jdg511/quadpreandrecorder/hardware/snapshots/hardware_snapshot_step1_before_via_resize_20260801_083059/manufacturing/QuadPreRecorder-drill-report.txt

Drill report for QuadPreRecorder.kicad_pcb
Created on 2026-07-25T09:17:04

Copper Layer Stackup:
    =============================================================
    L1 :  F.Cu                      front
    L2 :  B.Cu                      back

Drill file 'QuadPreRecorder-PTH.drl' contains
    plated through holes:
    =============================================================
    T1  0.400mm  0.0157"  (152 holes))
    T2  1.000mm  0.0394"  (137 holes)  (with 5 slots)
    T3  1.200mm  0.0472"  (4 holes))
    T4  1.300mm  0.0512"  (4 holes))
    T5  1.500mm  0.0591"  (8 holes)  (with 2 slots)
    T6  1.600mm  0.0630"  (3 holes))
    T7  1.850mm  0.0728"  (5 holes))

    Total plated holes count 313

Drill file 'QuadPreRecorder-NPTH.drl' contains
    unplated through holes:
    =============================================================
    T1  2.000mm  0.0787"  (2 holes))
    T2  3.000mm  0.1181"  (1 hole)
    T3  3.200mm  0.1260"  (8 holes))

    Total unplated holes count 11
