jdg511/quadpreandrecorder/hardware/QuadPreRecorder-enclosure-labeled-views.pdf

# QuadPreRecorder Rev C3

Enclosure preview with all ports and controls labeled. Hammond 1590XX, 145.2 x 121.2 x 39.3 mm.

### Illicit Apothecary

Face | Ref | Function
Lid | TFT | 3.5 inch capacitive touch display (MSP3526), near-flush window 85.5 x 56 mm
Lid | SW2 | Record button
Lid | SW3 | Rotary encoder, push + turn
Lid | SW4 | 5-way navigation switch (tilt 4 ways + press)
Front | J4 | 1/4 inch line output (Neutrik locking jack)
Front | D4 / D5 | Status LEDs (red / green)
Rear | J1 | 9 V DC input, barrel jack
Rear | J9 | USB-C, charging + data
Rear | SD | Micro-SD card slot (Teensy)
Left | J2 | CAT6 microphone input, shielded RJ45, 4 balanced channels + shield
Right | J5 | 3.5 mm headphone output

Positions are taken from the routed Rev C3 board. Wall-feature heights are approximate for illustration; drilling is done from the 1:1 printed templates, not from this document. An interactive 3D version of this model is available as an HTML file that opens in any web browser.

### Front three-quarter view

### Rear three-quarter view

### Top (lid controls and display)

### Front wall: J4 line out, D4/D5 status LEDs

### Rear wall: J1 9V DC, J9 USB-C, micro-SD

### Left wall: J2 CAT6 mic input

### Right wall: J5 headphone out
