jdg511/quadpreandrecorder/hardware/snapshots/hardware_snapshot_step1_before_via_resize_20260801_083059/exports/QuadPreRecorder-isometric.png

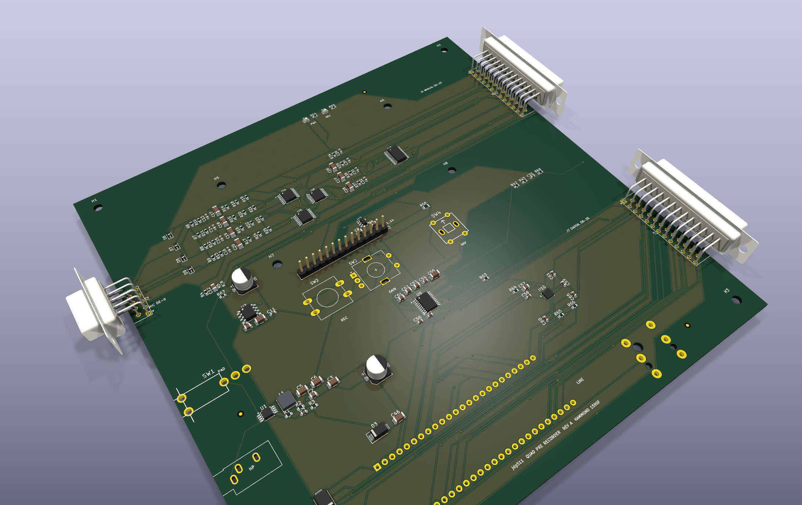
hardware/snapshots/hardware_snapshot_step1_before_via_resize_20260801_083059/exports/QuadPreRecorder-isometric.png
