jdg511/quadpreandrecorder/hardware/snapshots/hardware_snapshot_step1_before_via_resize_20260801_083059/manufacturing/QuadPreRecorder-assembly-bottom.pdf

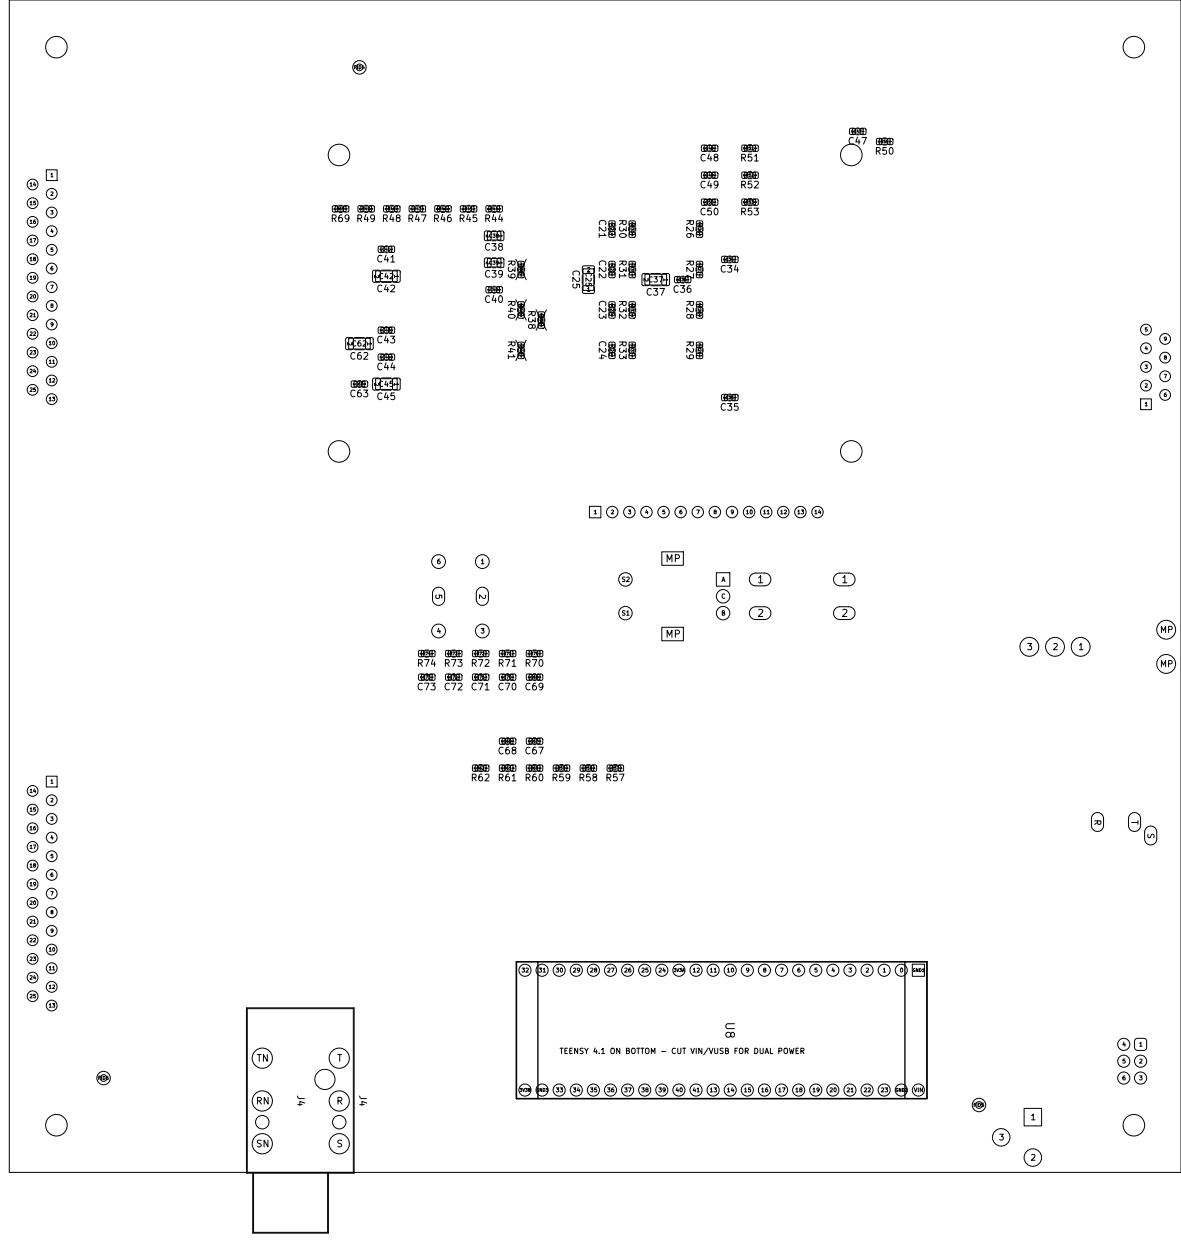
[picture p28: page 1]

1 TEENSY 4.1 ON BOTTOM - CUT VIN/VUSB FOR DUAL POWER
