jdg511/quadpreandrecorder/hardware/snapshots/hardware_snapshot_step1_before_via_resize_20260801_083059/manufacturing/QuadPreRecorder-assembly-top.pdf

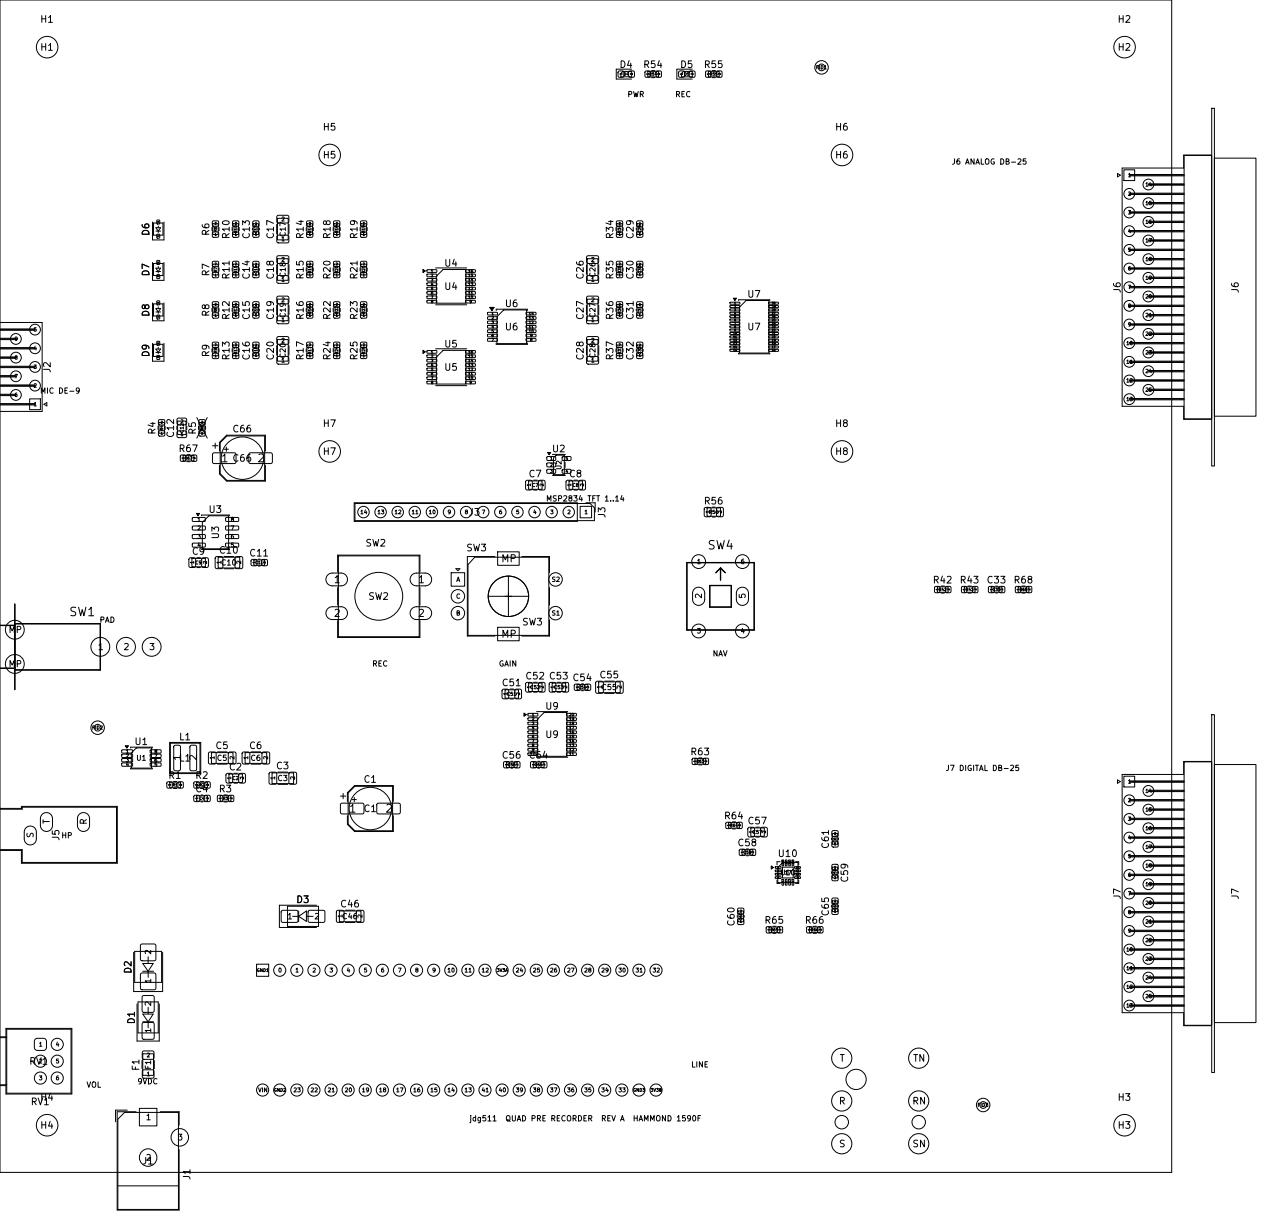
[picture p33: page 1]

jdg511 QUAD PRE RECORDER REV A HAMMOND 1590F
