jdg511/quadpreandrecorder/tools/build_manufacturing.py

"""Generate the checked PCBWay fabrication and assembly handoff.

This script intentionally depends only on Python's standard library and the
KiCad 10 command-line tools.  Run it from any directory with:

    python tools/build_manufacturing.py
"""

from __future__ import annotations

import csv
import hashlib
import os
from pathlib import Path
import shutil
import subprocess
import zipfile


ROOT = Path(__file__).resolve().parents[1]
HARDWARE = ROOT / "hardware"
SCHEMATIC = HARDWARE / "QuadPreRecorder.kicad_sch"
BOARD = HARDWARE / "QuadPreRecorder.kicad_pcb"
OUT = HARDWARE / "manufacturing"
GERBERS = OUT / "gerbers"
EXPORTS = HARDWARE / "exports"
FAB = HARDWARE / "fabrication"
KICAD_CLI = Path(os.environ.get("KICAD_CLI", "")) if os.environ.get("KICAD_CLI") else (
    Path(os.environ.get("LOCALAPPDATA", "")) / "Programs" / "KiCad" / "10.0" / "bin" / "kicad-cli.exe"
)


def run(*args: str, capture: bool = False) -> str:
    command = [str(KICAD_CLI), *args]
    result = subprocess.run(
        command,
        cwd=ROOT,
        check=True,
        text=True,
        capture_output=capture,
    )
    return result.stdout if capture else ""


def drc_is_manufacturing_acceptable(report: str) -> bool:
    """Allow only assembly-courtyard DRC errors; block electrical/fab issues."""

    if "Found 0 unconnected pads" not in report:
        return False
    violation_kinds = {
        line.split("]", 1)[0][1:]
        for line in report.splitlines()
        if line.startswith("[") and "]:" in line
    }
    return not violation_kinds or violation_kinds <= {"courtyards_overlap"}


def reset_generated_directory(path: Path) -> None:
    resolved = path.resolve()
    if ROOT.resolve() not in resolved.parents:
        raise RuntimeError(f"Refusing to reset path outside repository: {resolved}")
    if resolved.exists():
        shutil.rmtree(resolved)
    resolved.mkdir(parents=True)


def build_cpl() -> None:
    raw = OUT / "QuadPreRecorder-CPL-KiCad.csv"
    run(
        "pcb", "export", "pos", "--format", "csv", "--units", "mm",
        "--side", "both", "--exclude-dnp", "-o", str(raw), str(BOARD),
    )
    with raw.open(newline="", encoding="utf-8-sig") as source:
        rows = list(csv.DictReader(source))

    normalized = OUT / "QuadPreRecorder-CPL-PCBWay.csv"
    with normalized.open("w", newline="", encoding="utf-8-sig") as target:
        writer = csv.DictWriter(
            target,
            fieldnames=["Designator", "Mid X", "Mid Y", "Layer", "Rotation"],
        )
        writer.writeheader()
        for row in rows:
            writer.writerow({
                "Designator": row["Ref"],
                "Mid X": f'{float(row["PosX"]):.4f}mm',
                "Mid Y": f'{float(row["PosY"]):.4f}mm',
                "Layer": "Top" if row["Side"].lower() == "top" else "Bottom",
                "Rotation": f'{float(row["Rot"]):.2f}',
            })


# 2026-09-06: parts PCBWay must fit or supply that are NOT placement lines in
# the KiCad BOM/CPL - the U8 socket sub-assembly, and loose off-board parts to
# quote and ship with the boards. Written as a separate CSV so the CPL import
# is not confused by designators that have no placement.
EXTRA_PARTS: list[tuple[str, str, str, str, str, str]] = [
    # designator/role, description, manufacturer, MPN, qty per board, note
    ("U8 (socket)", "1x24 low-profile female socket strip, 2.54 mm, 4.57 mm profile",
     "Samtec", "SLW-124-01-G-S", "2",
     "Solder BOTH strips into the U8 footprint (bottom side, rows at 17.78 mm). "
     "Then plug the Teensy into them - see U8 (module)."),
    ("U8 (module)", "Teensy 4.1 WITH pins pre-soldered (outer 2x24 rows)",
     "PJRC", "TEENSY41_PINS", "1",
     "Plug into the two SLW-124 sockets, microSD slot toward the board edge marked "
     "'SD CARD SLOT THIS EDGE'. Customer-supplied if PCBWay cannot source PJRC. "
     "TEENSY41_NE_PINS (no Ethernet chip) is an acceptable substitute."),
    ("TFT (loose)", "LCDWiki MSP3526 3.5in IPS SPI TFT 320x480, ST7796U, FT6336U CAPACITIVE touch, 14-pin header",
     "LCDWiki / QDtech", "MSP3526", "1",
     "OFF-BOARD, ship loose - do NOT solder; it plugs into the J3 socket. NOT the "
     "MSP3520 (resistive). Please quote; customer will supply if unavailable."),
    ("TFT standoffs (loose)", "M3 x 11 mm brass standoff, female-female, + 8x M3x6 screws",
     "generic", "M3x11 F-F", "4",
     "OFF-BOARD, ship loose. Mounts the TFT over H5-H8 (socket 8.5 mm + header body 2.5 mm)."),
    ("USB D+/D- wires", "2x ~20 mm 30 AWG wire, TP1/TP2 (bottom) to the Teensy 4.1 underside 'USB Device' D+ / D- pads",
     "-", "-", "2",
     "ASSEMBLY STEP: solder the two wires to the Teensy's underside D+/D- pads and to TP1 (D+) / TP2 (D-) "
     "before plugging the Teensy into its sockets. Also CUT the Teensy's VIN-VUSB link pad. "
     "Keep the wires short and together."),
    ("Battery (loose, customer-supplied)", "3.7 V 1S LiPo pouch 906090 (9 x 60 x 90 mm) 5000 mAh WITH protection circuit (PCM) and JST-PH 2.0 mm pigtail",
     "generic", "LP906090 5000mAh PCM JST-PH", "1",
     "OFF-BOARD. Lithium cells usually cannot ship with the boards - customer will supply. Plugs into J10 (bottom, + on pin 1 - CHECK pigtail polarity), lies on the box floor under the right half of the board on foam tape."),
    ("PSU (loose)", "9 VDC 1 A regulated wall adapter, 5.5 x 2.1 mm barrel, CENTER POSITIVE, US plug",
     "generic", "9V/1A 5.5x2.1 center+", "1",
     "OFF-BOARD, ship loose. Mates with J1 (CUI PJ-102AH). Optional - the unit also runs from USB-C 5 V. Please quote."),
    ("USB-C cable (loose)", "USB-C to USB-C (or USB-A to USB-C) 2.0 cable, 1 m",
     "generic", "USB-C 2.0 cable", "1",
     "OFF-BOARD, ship loose. Please quote."),
    ("Knob SW3 (loose)", "Push-on knob for 6 mm 18-spline knurled shaft, ~Ø16-20 mm",
     "generic", "6 mm knurled push-on knob", "1",
     "OFF-BOARD, ship loose. For the Alps EC11E encoder. Please quote."),
    ("Keycap SW2 (loose)", "Round keycap for Omron B3F-5xxx 12 mm tactile switch",
     "Omron", "B32-1000 series", "1",
     "OFF-BOARD, ship loose. Please quote."),
]


def write_extras_bom() -> None:
    path = OUT / "QuadPreRecorder-BOM-extras.csv"
    with path.open("w", newline="", encoding="utf-8") as handle:
        writer = csv.writer(handle)
        writer.writerow(["Designator", "Comment", "Manufacturer", "Manufacturer Part Number", "Quantity", "Note"])
        for row in EXTRA_PARTS:
            writer.writerow(row)


def write_checksums() -> None:
    files = sorted(
        path for path in OUT.rglob("*")
        if path.is_file() and path.name != "SHA256SUMS.txt" and path.suffix != ".zip"
        and "RevA" not in path.name and "RevB" not in path.name and "Rev3" not in path.name and "REV3" not in path.name
        and not path.relative_to(OUT).as_posix().startswith("rev3-4layer/")
        and not path.relative_to(OUT).as_posix().startswith("revb-archive/")
    )
    lines = []
    for path in files:
        digest = hashlib.sha256(path.read_bytes()).hexdigest()
        lines.append(f"{digest}  {path.relative_to(OUT).as_posix()}")
    (OUT / "SHA256SUMS.txt").write_text("\n".join(lines) + "\n", encoding="ascii")


def make_zip(destination: Path, files: list[Path], base: Path) -> None:
    with zipfile.ZipFile(destination, "w", zipfile.ZIP_DEFLATED) as archive:
        for path in files:
            archive.write(path, path.relative_to(base).as_posix())


def main() -> None:
    if not KICAD_CLI.exists():
        raise RuntimeError(f"kicad-cli not found: {KICAD_CLI}")
    for required in (SCHEMATIC, BOARD):
        if not required.exists():
            raise FileNotFoundError(required)

    OUT.mkdir(parents=True, exist_ok=True)
    EXPORTS.mkdir(parents=True, exist_ok=True)
    FAB.mkdir(parents=True, exist_ok=True)
    reset_generated_directory(GERBERS)

    run("sch", "erc", "--severity-all", "-o", str(FAB / "QuadPreRecorder-erc.rpt"), str(SCHEMATIC))
    run(
        "pcb", "drc", "--all-track-errors", "--schematic-parity", "--severity-error",
        "-o", str(FAB / "QuadPreRecorder-drc.rpt"), str(BOARD),
    )
    erc = (FAB / "QuadPreRecorder-erc.rpt").read_text(encoding="utf-8-sig")
    drc = (FAB / "QuadPreRecorder-drc.rpt").read_text(encoding="utf-8-sig")
    if "ERC messages: 0  Errors 0  Warnings 0" not in erc:
        raise RuntimeError("ERC is not clean; fabrication package not generated")
    if not drc_is_manufacturing_acceptable(drc):
        raise RuntimeError("DRC has electrical/fabrication errors; fabrication package not generated")

    run(
        "pcb", "export", "gerbers", "--check-zones", "--subtract-soldermask",
        "--layers", "F.Cu,In1.Cu,In2.Cu,B.Cu,F.Paste,B.Paste,F.Mask,B.Mask,F.Silkscreen,B.Silkscreen,Edge.Cuts",
        "-o", str(GERBERS), str(BOARD),
    )
    run("pcb", "export", "ipcd356", "-o", str(GERBERS / "QuadPreRecorder.d356"), str(BOARD))
    run(
        "pcb", "export", "drill", "--format", "excellon", "--excellon-units", "mm",
        "--excellon-zeros-format", "decimal", "--excellon-separate-th", "--generate-map",
        "--map-format", "pdf", "--generate-report",
        "--report-path", str(OUT / "QuadPreRecorder-drill-report.txt"),
        "-o", str(GERBERS), str(BOARD),
    )

    run(
        "sch", "export", "bom", "-o", str(OUT / "QuadPreRecorder-BOM.csv"),
        "--fields", "Reference,Value,Footprint,Manufacturer,MPN,Datasheet,QUANTITY,DNP",
        "--labels", "Designator,Comment,Footprint,Manufacturer,Manufacturer Part Number,Datasheet,Quantity,DNP",
        "--group-by", "Value,Footprint,Manufacturer,MPN,DNP", "--sort-field", "Reference",
        str(SCHEMATIC),
    )
    build_cpl()
    write_extras_bom()

    run("sch", "export", "pdf", "-o", str(EXPORTS / "QuadPreRecorder-schematic.pdf"), str(SCHEMATIC))
    run(
        "pcb", "export", "pdf", "--mode-single", "--black-and-white", "--scale", "1",
        "--sketch-pads-on-fab-layers", "--crossout-DNP-footprints-on-fab-layers",
        "--layers", "F.Fab,F.Silkscreen,Edge.Cuts", "-o", str(OUT / "QuadPreRecorder-assembly-top.pdf"), str(BOARD),
    )
    run(
        "pcb", "export", "pdf", "--mode-single", "--black-and-white", "--scale", "1", "--mirror",
        "--sketch-pads-on-fab-layers", "--crossout-DNP-footprints-on-fab-layers",
        "--layers", "B.Fab,B.Silkscreen,Edge.Cuts", "-o", str(OUT / "QuadPreRecorder-assembly-bottom.pdf"), str(BOARD),
    )
    run(
        "pcb", "export", "pdf", "--mode-single", "--scale", "1", "--check-zones",
        "--layers", "F.Cu,F.Mask,F.Silkscreen,Edge.Cuts",
        "-o", str(EXPORTS / "QuadPreRecorder-top.pdf"), str(BOARD),
    )
    run(
        "pcb", "export", "pdf", "--mode-single", "--scale", "1", "--mirror", "--check-zones",
        "--layers", "B.Cu,B.Mask,B.Silkscreen,Edge.Cuts",
        "-o", str(EXPORTS / "QuadPreRecorder-bottom.pdf"), str(BOARD),
    )
    run(
        "pcb", "export", "svg", "--mode-single", "--fit-page-to-board", "--exclude-drawing-sheet",
        "--check-zones", "--layers", "F.Cu,F.Mask,F.Silkscreen,Edge.Cuts",
        "-o", str(EXPORTS / "QuadPreRecorder-top.svg"), str(BOARD),
    )
    run(
        "pcb", "export", "svg", "--mode-single", "--fit-page-to-board", "--exclude-drawing-sheet",
        "--mirror", "--check-zones", "--layers", "B.Cu,B.Mask,B.Silkscreen,Edge.Cuts",
        "-o", str(EXPORTS / "QuadPreRecorder-bottom.svg"), str(BOARD),
    )
    run(
        "pcb", "export", "step", "--force", "--no-dnp", "--subst-models",
        "-o", str(OUT / "QuadPreRecorder-RevC.step"), str(BOARD),
    )
    for side in ("top", "bottom"):
        run(
            "pcb", "render", "--side", side, "--quality", "high", "--background", "opaque",
            "--width", "2200", "--height", "1400",
            "-o", str(EXPORTS / f"QuadPreRecorder-{side}.png"), str(BOARD),
        )
    run(
        "pcb", "render", "--quality", "high", "--background", "opaque", "--perspective", "--floor",
        "--rotate", "-35,0,35", "--width", "2200", "--height", "1400",
        "-o", str(EXPORTS / "QuadPreRecorder-isometric.png"), str(BOARD),
    )

    run(
        "pcb", "export", "stats", "--format", "report", "--units", "mm",
        "-o", str(OUT / "QuadPreRecorder-board-stats.txt"), str(BOARD),
    )
    shutil.copy2(FAB / "QuadPreRecorder-erc.rpt", OUT / "QuadPreRecorder-erc.rpt")
    shutil.copy2(FAB / "QuadPreRecorder-drc.rpt", OUT / "QuadPreRecorder-drc.rpt")
    shutil.copy2(EXPORTS / "QuadPreRecorder-schematic.pdf", OUT / "QuadPreRecorder-schematic.pdf")
    shutil.copy2(HARDWARE / "connector-pinout.md", OUT / "connector-pinout.md")
    shutil.copy2(HARDWARE / "mechanical.md", OUT / "mechanical.md")

    gerber_files = sorted(path for path in GERBERS.iterdir() if path.is_file() and path.suffix.lower() != ".pdf")
    make_zip(OUT / "QuadPreRecorder-RevC-Gerbers.zip", gerber_files, GERBERS)
    write_checksums()
    # 2026-09-08 (Rev C): exclude the retired Rev A/B outputs and
    # the out-of-scope Rev3 4-layer files that also live in this folder, so the
    # PCBWay handoff only contains the current board.
    def _excluded(path: Path) -> bool:
        rel = path.relative_to(OUT).as_posix()
        name = path.name
        return (
            name == "QuadPreRecorder-RevC-PCBWay-handoff.zip"
            or "RevA" in name
            or "RevB" in name
            or "Rev3" in name
            or "REV3" in name
            or rel.startswith("rev3-4layer/")
            or rel.startswith("revb-archive/")
        )
    handoff_files = [
        path for path in OUT.rglob("*")
        if path.is_file() and not _excluded(path)
    ]
    make_zip(OUT / "QuadPreRecorder-RevC-PCBWay-handoff.zip", handoff_files, OUT)

    print(f"Manufacturing package: {OUT}")


if __name__ == "__main__":
    main()
